Vishalbabu-09/Auralab_Workstation/Auralab_Workstation/Auralab_Workstation Images/Layer-2(In1.Cu) GND, GNDA Plane).jpg

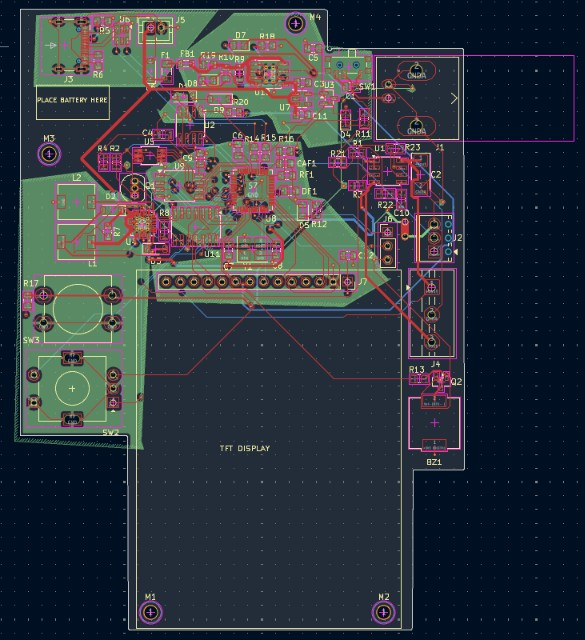
Auralab_Workstation/Auralab_Workstation Images/Layer-2(In1.Cu) GND, GNDA Plane).jpg
